ImoogDi/2MoreVO/doc/pictures/Backplane_B_bot.png

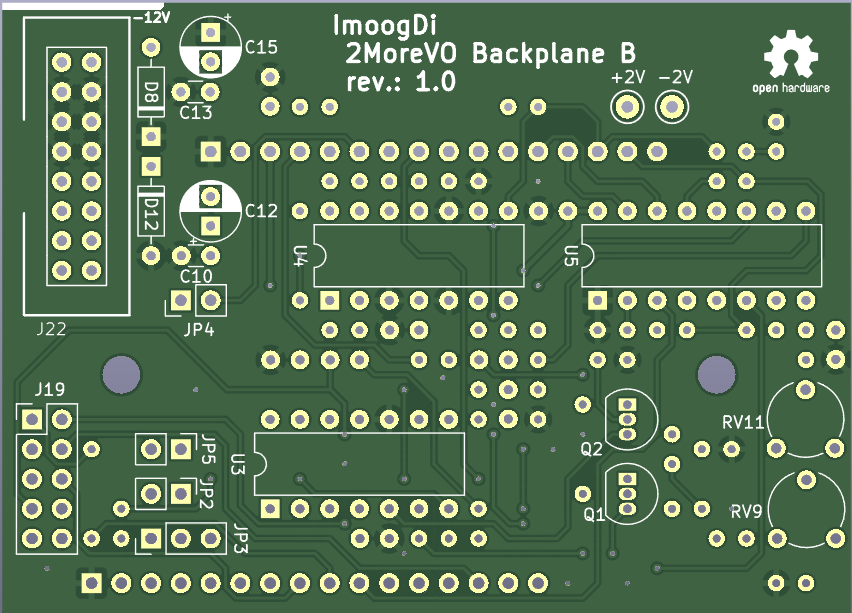
doc/pictures/Backplane_B_bot.png
