ImoogDi/2MoreVO/doc/pictures/Backplane_B_top.png

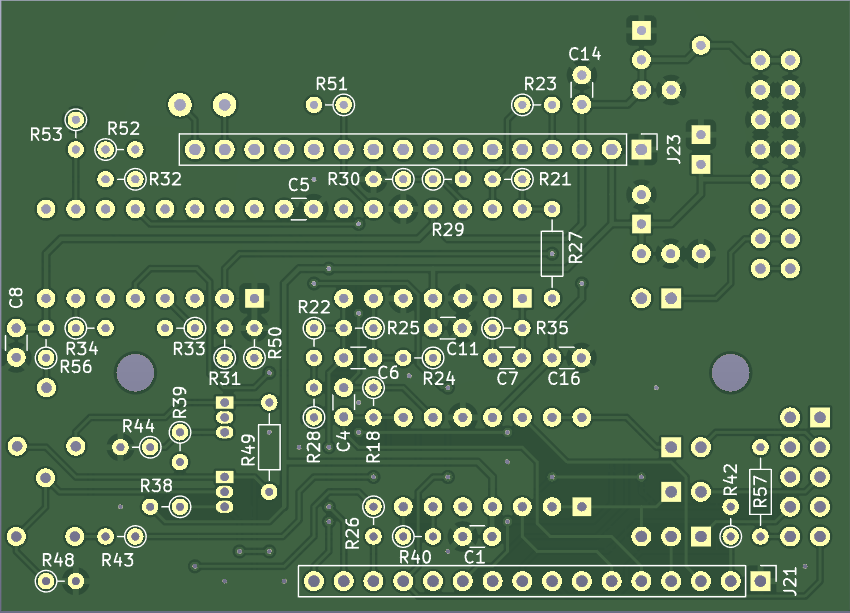
doc/pictures/Backplane_B_top.png
