ImoogDi/2MoreVO/doc/pictures/Backplane_spacer.png

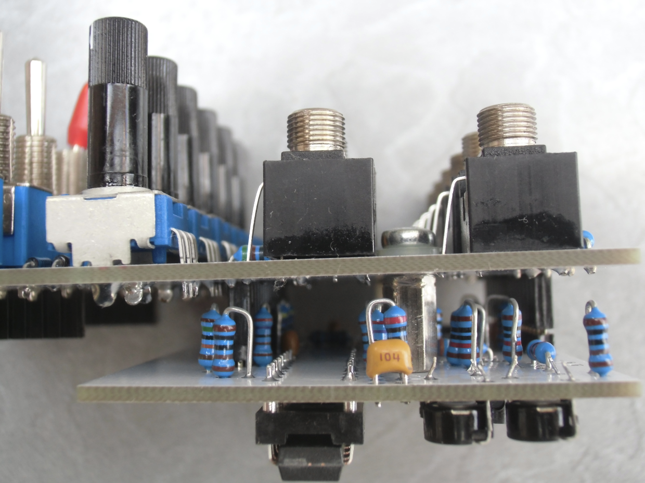
doc/pictures/Backplane_spacer.png
