ImoogDi/2MoreVO/doc/pictures/MoreVO_Core_PCB_top.png

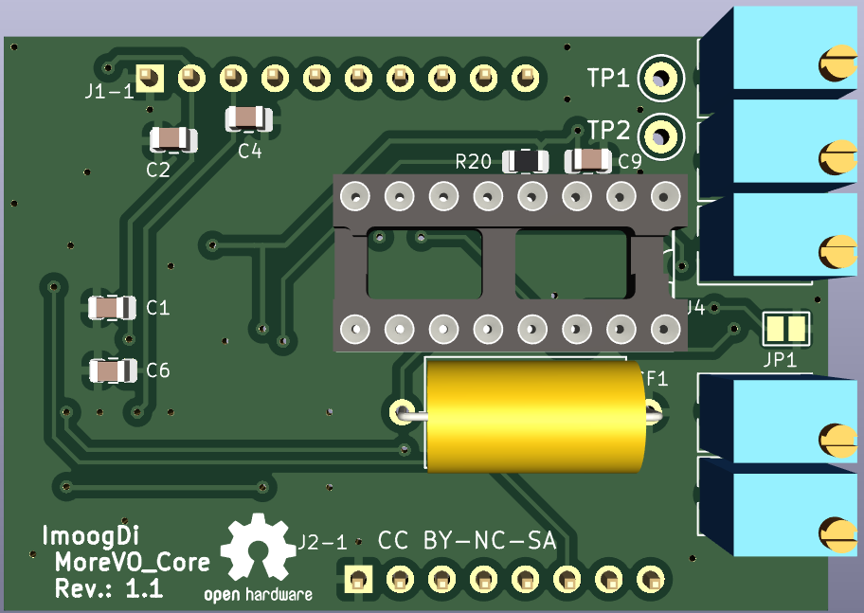
doc/pictures/MoreVO_Core_PCB_top.png
