ImoogDi/2MoreVO/doc/pictures/Backplane_B_top_parts_mounted.png

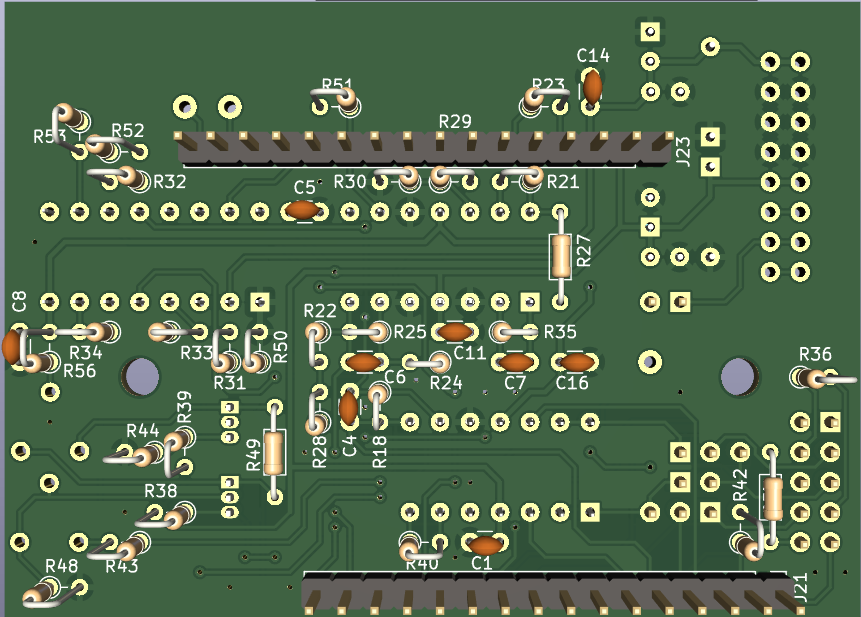
doc/pictures/Backplane_B_top_parts_mounted.png
